telzo2000/ckb4/img/img00003.jpg

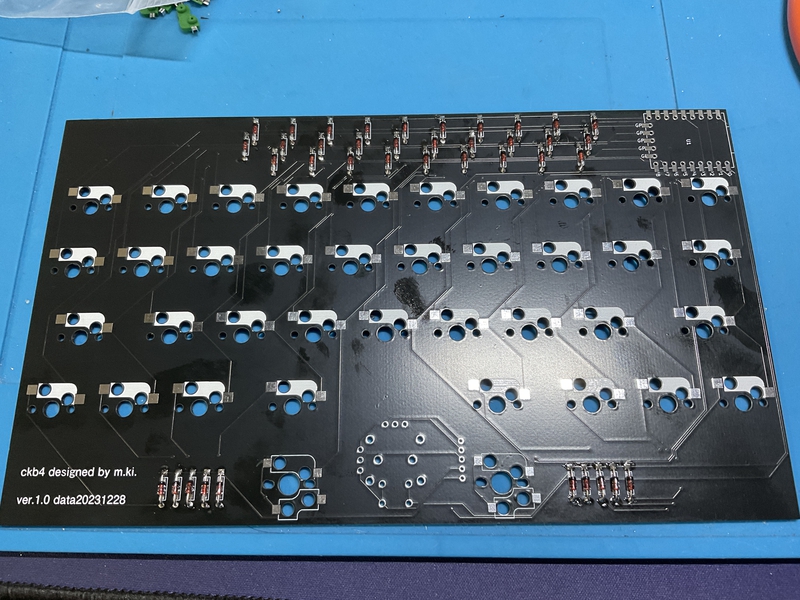
img/img00003.jpg
