telzo2000/ckb4/img/img00004.jpg

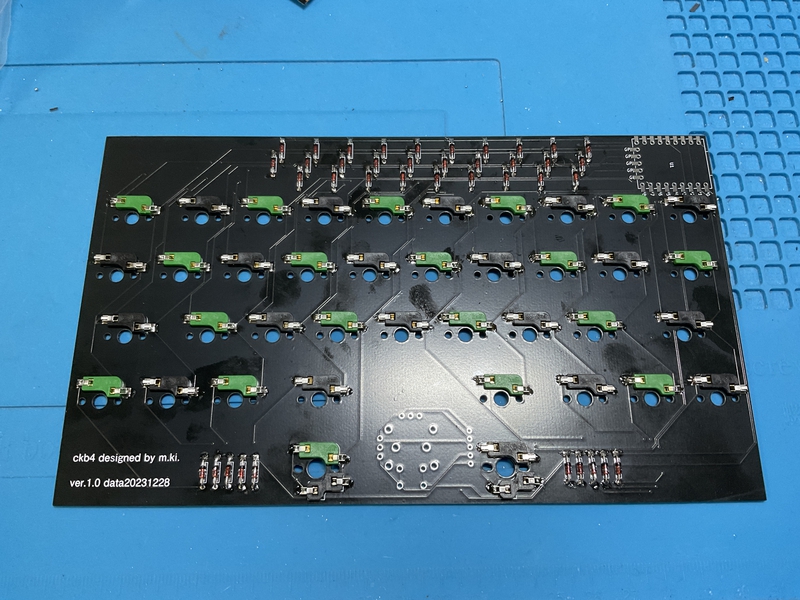
img/img00004.jpg
