telzo2000/ckb4/firmware/ckb4ura/keymaps/vial/config.h

// Copyright 2023 m.ki (@telzo2000)
// SPDX-License-Identifier: GPL-2.0-or-later

#pragma once
#define VIAL_KEYBOARD_UID {0x22, 0x43, 0xD2, 0xF7, 0xFF, 0x8D, 0x79, 0x73}
#define VIAL_UNLOCK_COMBO_ROWS { 0, 1 }
#define VIAL_UNLOCK_COMBO_COLS { 0, 1 }
